MarcinWachowiak/semiconductor-radiation-detector/LTspice_simulations/Gamma_pin_sim.asc

B2: bv; V=white(3e8*time)/1.1e2
C1: cap; 100p
C2: cap; 160p
C3: cap; 160p
C4: cap; 0.5p
C5: cap; 200p
C6: cap; 200p
C7: cap; 100n
C8: cap; 100n
C9: cap; 180p
C10: cap; 100n
C11: cap; 470p
C12: cap; 1p
C13: cap; 180p
C14: cap; 1n
C15: cap; 4,7u
C16: cap; 4.7µ
C17: cap; 4.7µ
C18: cap; 4.7µ
C19: cap; 22p
D1: schottky; BAS40-04HM
D2: schottky; BAS40-04HM
D3: schottky; BAS40-04HM
D4: schottky; BAS40-04HM
D5: schottky; BAS40-04HM
D6: schottky; BAS40-04HM
D7: schottky; BAS40-04HM
I1: current; PULSE(0 8n 100n 1n 100n 100n 50u 20)
I2: current; 20n
J1: njf; CPH3910N
R1: res; 470k
R2: res; 1k
R3: res; 6.2k
R4: res; 18k
R5: res; 6.8k
R6: res; 3k
R7: res; 510
R8: res; 100
R9: res; 1k
R10: res; 1k
R11: res; 33k
R12: res; 9.1k
R13: res; 33k
R14: res; 1.8k
R15: res; 4.7k; tol=1 pwr=0.1
R16: res; 1.6k
R17: res; 10Meg
R18: res; 4.7k; tol=1 pwr=0.1
R19: res; 300
R20: res; 1.6k
R21: res; 3.3k
R22: res; 1.6k
R23: res; 1.6k
R24: res; 1k
R25: res; 100
R26: res; 100
R27: res; 100
R28: res; 1
R29: res; 100
R30: res; 100
R31: res; 1k
R32: res; 22k
R33: res; 3.6k
R34: res; 30k
R35: res; 8.2k
R36: res; 100k
R37: res; 500
R38: res; 20
R39: res; 20k
R40: res; 2k
R41: res; 100
R42: res; 20k
R43: res; 20k
R44: res; 100
R45: res; 100
R46: res; 1k
R47: res; 1k
R48: res; 100
R49: res; 100
R50: res; 92
R52: res; 10
R53: res; 2.2k
R54: res; 3.3k
R55: res; 100
U1: LTC6268
U2: AD8066
U3: ADG701
U4: AD8066
U5: AD8066
U7: opamp2; ADA4898
U8: LT1713
U9: LT1713
U10: AD8066
U11: AD8066
U12: LTC6228
U13: opamp2; ADA4898
U14: opamp2; ADA4898
U15: opamp2; ADA4898
V1: voltage; 32V
V2: voltage; 5
V3: voltage; -5
V4: voltage; PULSE(0 5 40u 100n 100n 1u 50u 10)
Named nets: 0, VCC, VSS, Vbias, Rising_slope_detector, Pulse_duration, ADC, Fast_filter_output, TIA, Subtractor, Filters_output, Baseline_restorer, Differentiation_amplifier, Comparator_inverter
.tran 300u
Dark reverse current
Radiation pulses
ANALYSIS:
External dependencies:
Peak detector reset signal
PHOTODIODE
BOOTSTRAP
TRANSIMPEDANCE
AMPLIFIER
POWER
SUPPLY
SIMULATION PRESET
BASELINE RESTORER 
ANTI-PILEUP
SENSITIVE
DIFFERENTIATIOR
AMPLIFIER
INVERTING COMPARATOR 
WITH HYSTERESIS
NON-INVERTING
COMPARATOR
WITH HYSTERESIS
FAST PEAK DETECTOR WITH RESET
INVERTING AMPLIFIER
WITH DC OFFSET 
CANCELLATION
(SUBSTRACTOR)
INVERTER 
WITH AC
COUPLING
.lib E:\\Programy\\LTSpice\\lib\\sub\\ADA4898.sub
GAUSSIAN PULSE SHAPER, SECOND ORDER BESSEL FILTER, SALLEN-KEY TOPOLOGY
LOW PASS FILTER 50kHz
.options gmin=1e-10 
.options abstol=1e-10 
.options reltol=0.003 
.options cshunt=1e-15
Exact values of components are yet to
be adjusted for optimal readings of the detector
